CWempe/Thermostat-Controller/Fritzing/Thermostat-Controller_pcb_bottom.png

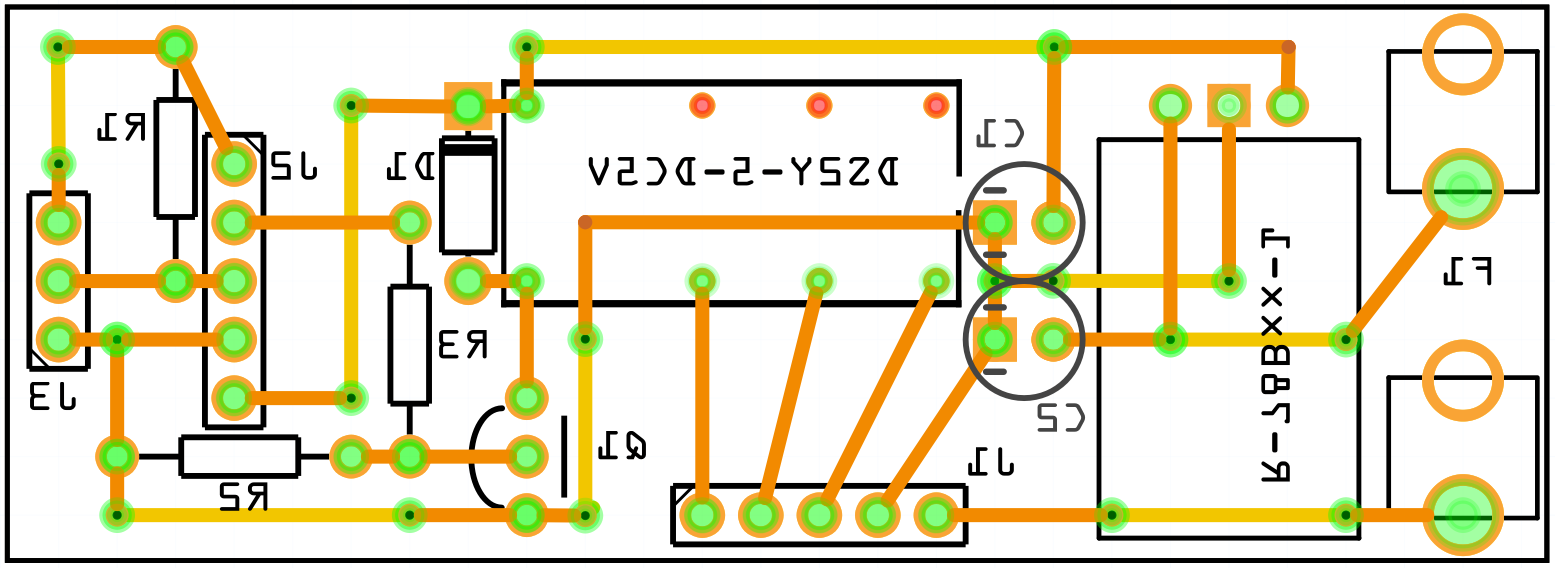
Fritzing/Thermostat-Controller_pcb_bottom.png
