CWempe/Thermostat-Controller/photos/photo_arduino_with_cable.jpg

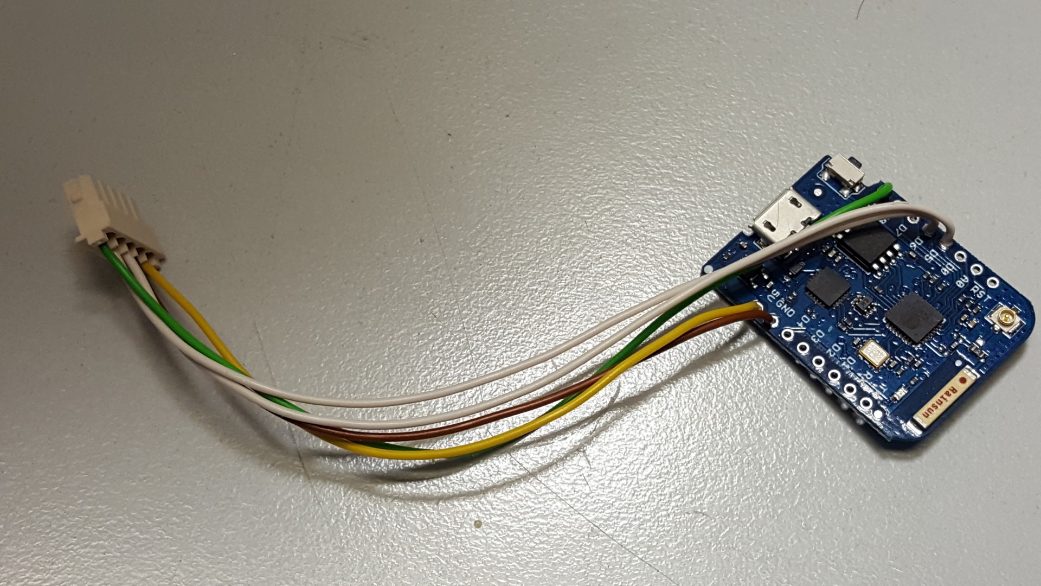
photos/photo_arduino_with_cable.jpg
